craftbrak/ELec2T/CCS/common.h

#include <18F458.h>
#device adc=8

#FUSES NOWDT                    //No Watch Dog Timer
#FUSES WDT128                   //Watch Dog Timer uses 1:128 Postscale
#FUSES RC_IO                    //Resistor/Capacitor Osc
#FUSES NOPROTECT                //Code not protected from reading
#FUSES NOOSCSEN                 //Oscillator switching is disabled, main oscillator is source
#FUSES BROWNOUT                 //Reset when brownout detected
#FUSES BORV20                   //Brownout reset at 2.0V
#FUSES NOPUT                    //No Power Up Timer
#FUSES NOCPD                    //No EE protection
#FUSES STVREN                   //Stack full/underflow will cause reset
#FUSES NODEBUG                  //No Debug mode for ICD
#FUSES LVP                      //Low Voltage Programming on B3(PIC16) or B5(PIC18)
#FUSES NOWRT                    //Program memory not write protected
#FUSES NOWRTD                   //Data EEPROM not write protected
#FUSES NOWRTB                   //Boot block not write protected
#FUSES NOCPB                    //No Boot Block code protection
#FUSES NOWRTC                   //configuration not registers write protected
#FUSES NOEBTR                   //Memory not protected from table reads
#FUSES NOEBTRB                  //Boot block not protected from table reads

#use delay(clock=20000000)
#use rs232(baud=9600,parity=N,xmit=PIN_C6,rcv=PIN_C7,bits=8)

#define FLAG_RESET   1
#define FLAG_RESEND  2
#define FLAG_SET_MAX 4

#define BUFFER_SIZE  2
